JensFZ/CO2Sensor_PCB/Images/CO2Sensor V1.0 - 5.jpg

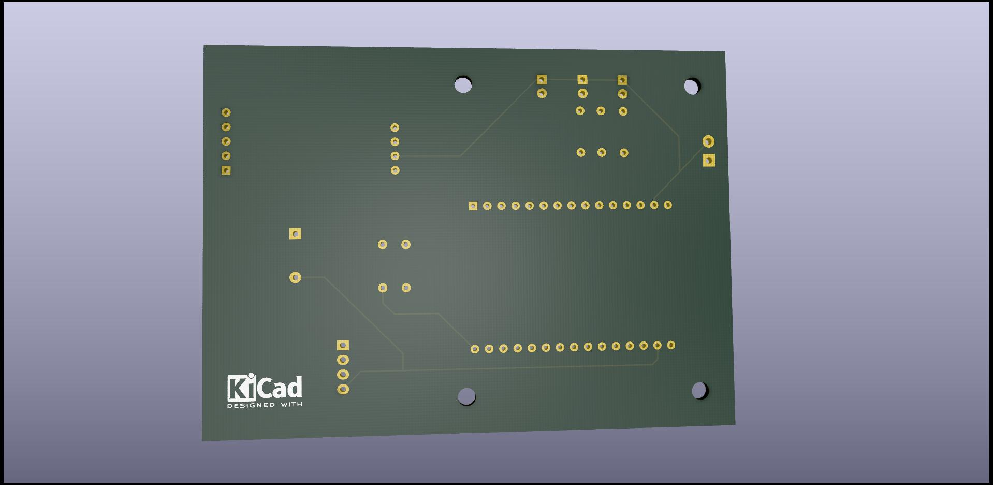
Images/CO2Sensor V1.0 - 5.jpg
