JensFZ/CO2Sensor_PCB/Images/IMG_6241.jpg

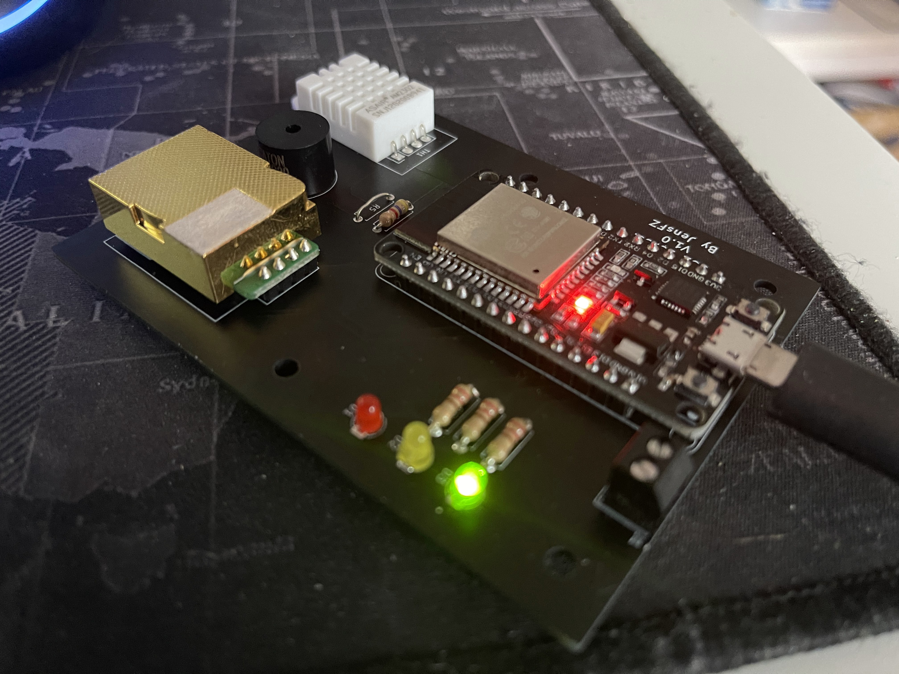
Images/IMG_6241.jpg
