JensFZ/CO2Sensor_PCB/Images/IMG_6242.jpg

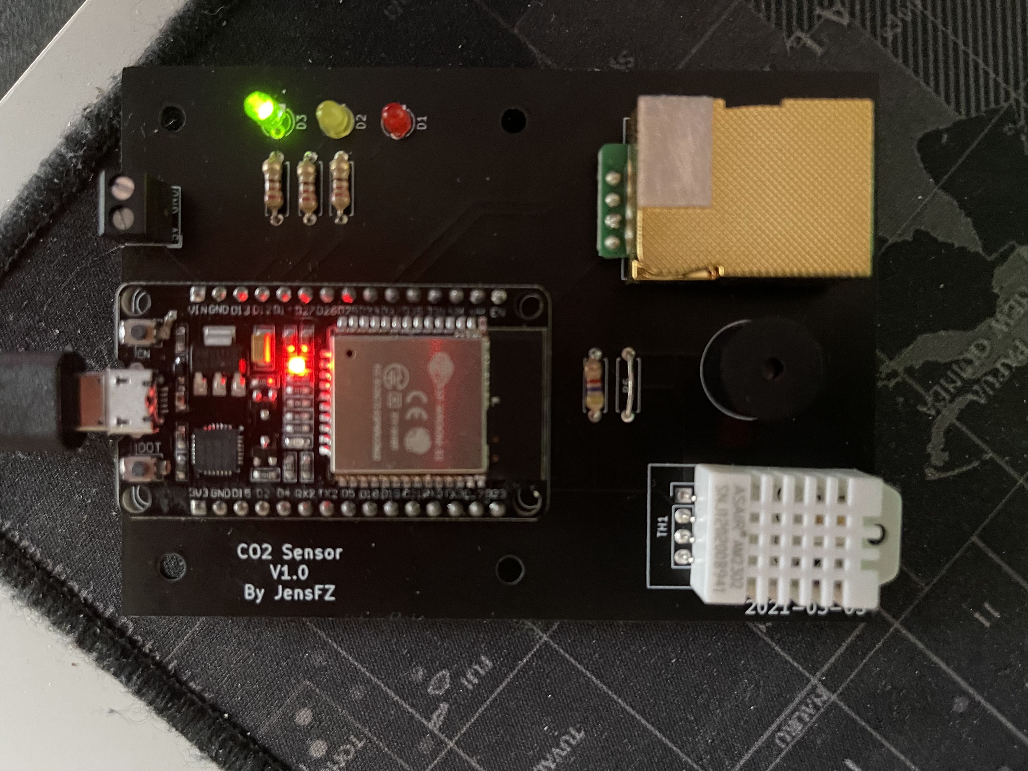
Images/IMG_6242.jpg
